ksmonkey123/eeprom-programmer/firmware/src/communications.cpp

#include "../include/communications.h"
#include "../include/status_indicator.h"

static void initCommunications(HardwareSerial &serial) {
    serial.begin(230400);
    leds::indicateConnected();
}

static int consumeUntilNextLineBreak(HardwareSerial &serial);

static char readNextCharBlocking(HardwareSerial &serial);

Communications::Communications(HardwareSerial &channel) : channel(channel) {
    initCommunications(channel);
}

Print &Communications::getOutput() const { return channel; }

static void log_command_buffer_overflow(HardwareSerial &channel, char const *buffer, const int limit,
                                        const int overflow) {
    channel.print(F("-SYNTAX ERROR: COMMAND BUFFER OVERFLOW: "));
    for (int i = 0; i < limit; i++) {
        channel.print(buffer[i]);
    }

    channel.print(F("... ("));
    channel.print(overflow);
    channel.println(F(" more chars)"));
}

int Communications::receiveNextCommand(char *buffer, const int limit) const {
    int buffer_length = 0;
    while (true) {
        const char c = readNextCharBlocking(channel);

        if (c != '\n') {
            // if buffer already full, we need to throw everything out.
            if (buffer_length < limit) {
                // write into buffer.
                buffer[buffer_length++] = c;
            } else {
                leds::setErrorIndicator(true);
                const int overflow = consumeUntilNextLineBreak(channel);
                log_command_buffer_overflow(channel, buffer, limit, overflow);
                buffer_length = 0;
            }
            continue;
        }

        // we have a new line, pre-parse command.
        if (buffer[0] == 'S' && buffer[1] == 'Y' && buffer[2] == 'N' && buffer_length == 3) {
            // handle sync directly.
            channel.println(F("*"));
            // reset buffer
            buffer_length = 0;
            continue;
        }

        if (buffer_length == 0) {
            channel.println(F("-INVALID COMMAND: EMPTY LINE"));
            continue;
        }

        return buffer_length;
    }
}

// helper functions
static char readNextCharBlocking(HardwareSerial &serial) {
    while (true) {
        if (serial.available() == 0) {
            // use idle time waiting on new data for seeding the RNG
            random();

            continue;
        }

        // we have data (ignore null char and \r)
        const auto c = static_cast<char>(serial.read());
        if (c == 0 || c == '\r' || c == ' ') {
            continue;
        }

        return c;
    }
}

static int consumeUntilNextLineBreak(HardwareSerial &serial) {
    int counter = 1;
    while (true) {
        const char c = readNextCharBlocking(serial);
        if (c == '\n') {
            return counter;
        }
        counter++;
    }
}
