ksmonkey123/eeprom-programmer/firmware/include/rom_interface.h

#pragma once
#include "common.h"

enum RomInterfaceState { IDLE, READ, WRITE };

class RomInterface {
    RomInterfaceState state;

public:
    explicit RomInterface();

    ~RomInterface();

    byte read(address address);

    void write(address address, byte data);
};
