ksmonkey123/eeprom-programmer/firmware/src/status_indicator.h

#pragma once
#include <Arduino.h>

namespace leds {
void setActiveIndicator(bool state);
void setErrorIndicator(bool state);
void setWriteIndicator(bool state);

void indicateConnected();
}  // namespace leds
