ksmonkey123/eeprom-programmer/firmware/src/utils.cpp

#include "../include/utils.h"

static byte hexCharToHalfByte(const char input) {
    switch (input) {
        case '0':
            return 0;
        case '1':
            return 1;
        case '2':
            return 2;
        case '3':
            return 3;
        case '4':
            return 4;
        case '5':
            return 5;
        case '6':
            return 6;
        case '7':
            return 7;
        case '8':
            return 8;
        case '9':
            return 9;
        case 'A':
            return 10;
        case 'B':
            return 11;
        case 'C':
            return 12;
        case 'D':
            return 13;
        case 'E':
            return 14;
        case 'F':
            return 15;
        default:
            return 255;
    }
}

bool hexToByte(const char *input, byte *dest) {
    const byte high = hexCharToHalfByte(input[0]);
    const byte low = hexCharToHalfByte(input[1]);

    if (high == 255 || low == 255) {
        return false;
    }

    *dest = ((high << 4) & 0xf0) + (low & 0x0f);
    return true;
}

bool hexToAddress(const char *input, address *dest) {
    address result = 0;
    for (byte i = 0; i < 4; i++) {
        const byte nextHalfByte = hexCharToHalfByte(input[i]);
        if (nextHalfByte == 255) {
            return false;
        }

        result = ((result << 4) & 0xfff0) | (nextHalfByte & 0x000f);
    }

    // addresses are only valid up to 0x7fff. If the leading bit is 1, we treat
    // it as bad.
    if (result > 0x7fff) {
        return false;
    }
    *dest = result;
    return true;
}

void printData(const byte value, Print &output) {
    if (value < 0x10) {
        output.print('0');
    }
    output.print(value, HEX);
}

void printAddress(const address value, Print &output) {
    if (value < 0x1000) {
        output.print('0');
    }
    if (value < 0x0100) {
        output.print('0');
    }
    if (value < 0x0010) {
        output.print('0');
    }
    output.print(value, HEX);
}
